yuveerrajpal/VeloGuard/analysis/output/phase_distributions.png

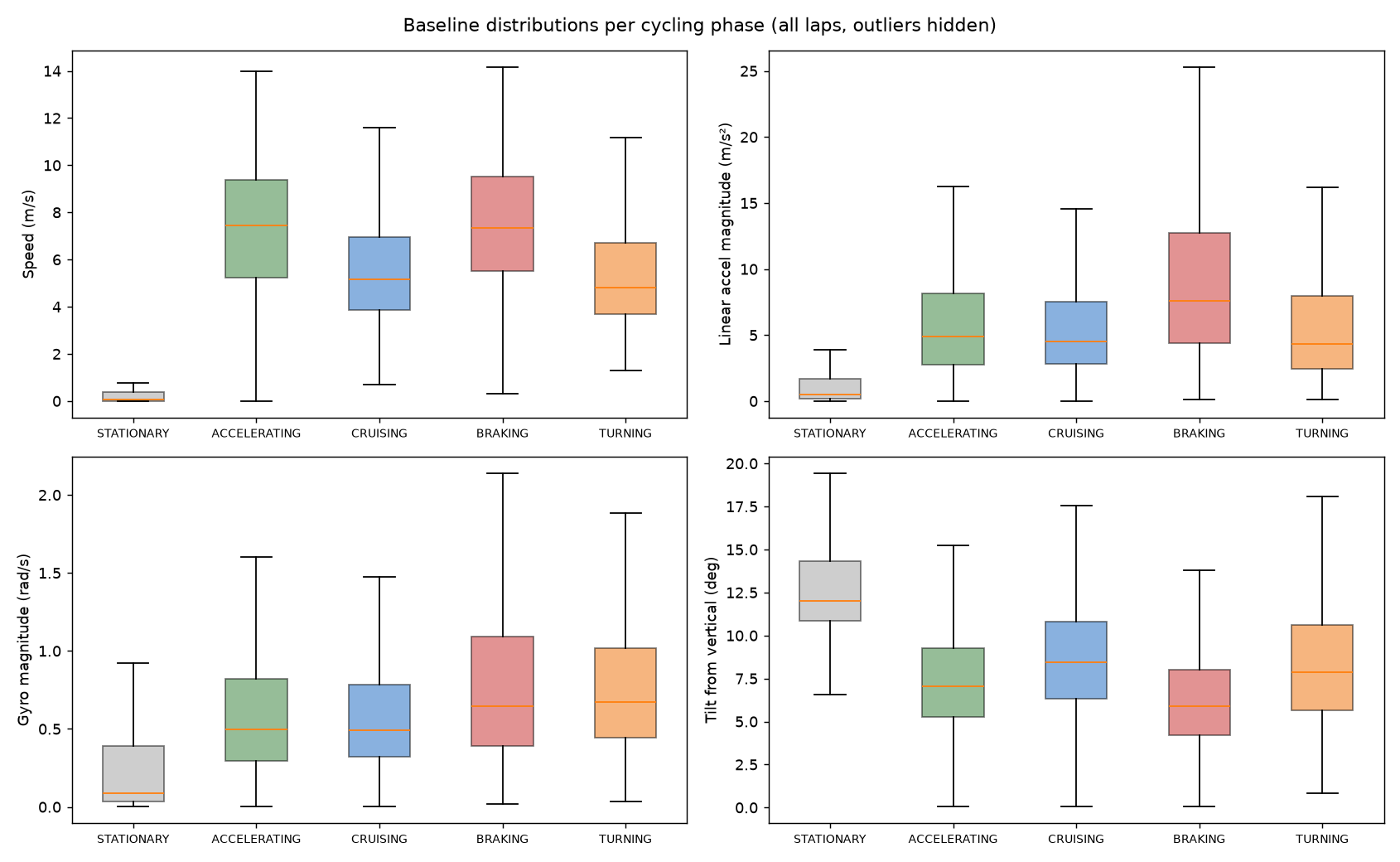
analysis/output/phase_distributions.png
